01ive/arduino_variometer/vario/accelerometer.h

#include <Adafruit_MPU6050.h>
#include <Wire.h>

class Accelerometer_Sensor : public Adafruit_MPU6050 {
    public:
        typedef enum return_code {
            ACCEL_SENSOR_OK = 0,
            ACCEL_SENSOR_FAIL = 1
        }t_return_code;

        Accelerometer_Sensor::Accelerometer_Sensor(TwoWire *);
        Accelerometer_Sensor::t_return_code Accelerometer_Sensor::start_up();
        Accelerometer_Sensor::tick();

        sensors_vec_t Accelerometer_Sensor::readAcceleration();
        sensors_vec_t Accelerometer_Sensor::readGyroscope();
        float Accelerometer_Sensor::readTemperature();
        float Accelerometer_Sensor::getAccelerationNormal();
    
    private:
        TwoWire *_pI2c;
        sensors_event_t _accel, _gyro, _temp;
};
